JonathanXLin/SmartSwitch/photos/raw/DSC_2327.JPG

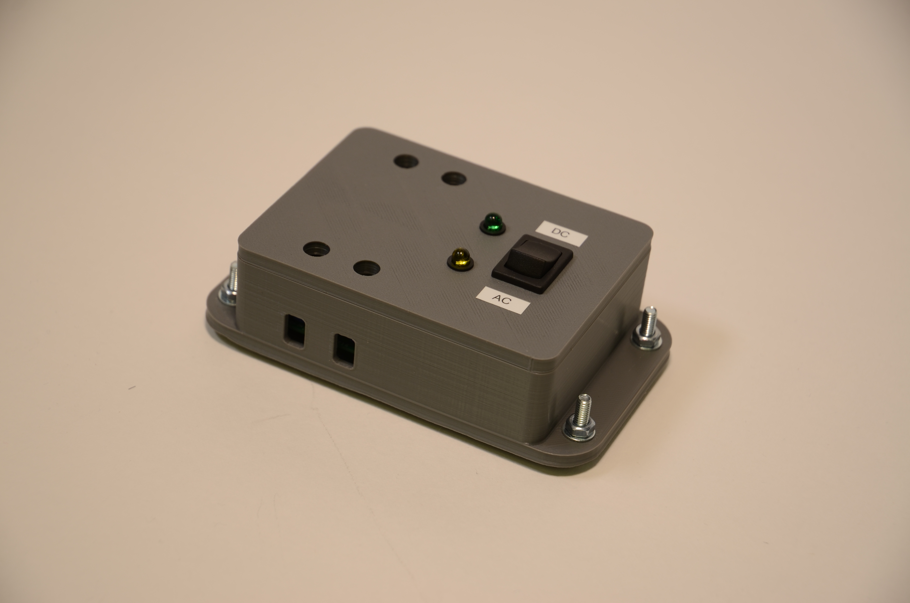
photos/raw/DSC_2327.JPG
