JonathanXLin/SmartSwitch/photos/raw/DSC_2328.JPG

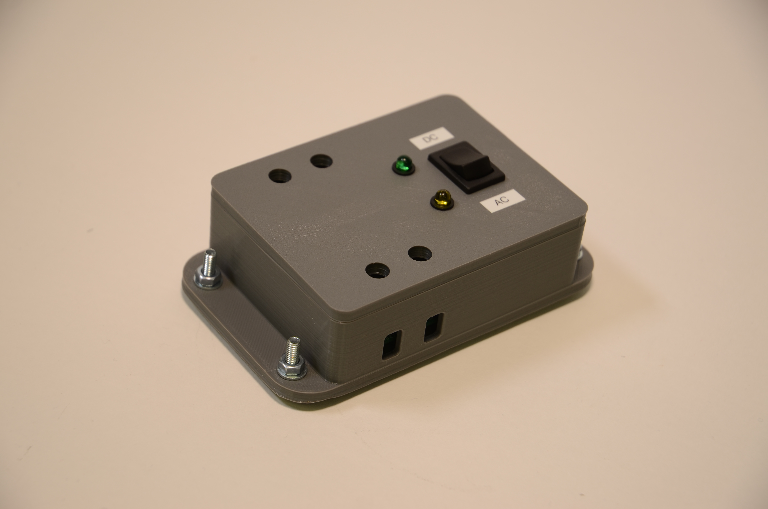
photos/raw/DSC_2328.JPG
