JonathanXLin/SmartSwitch/photos/raw/DSC_2329.JPG

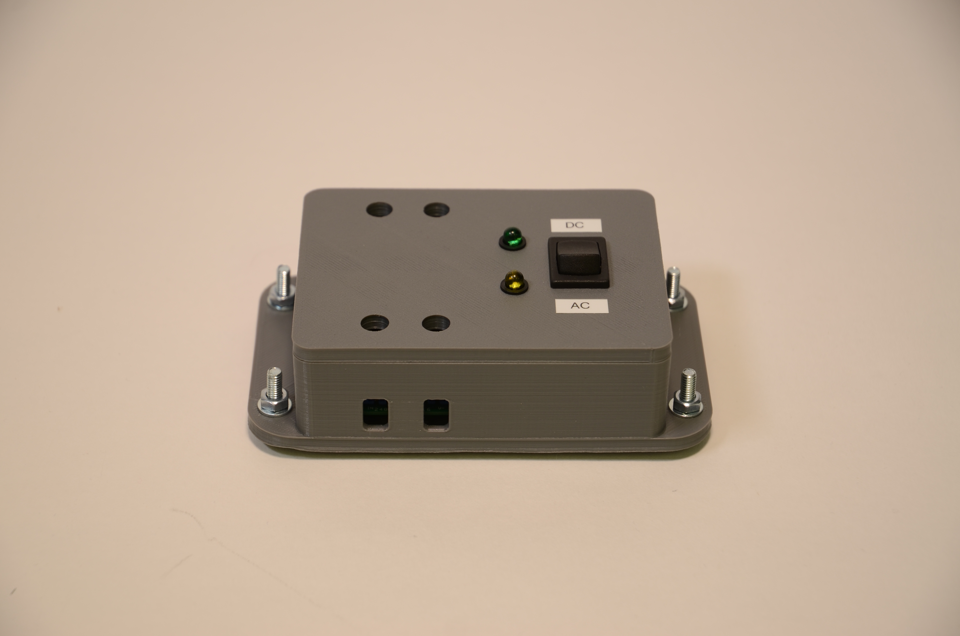
photos/raw/DSC_2329.JPG
