JonathanXLin/SmartSwitch/photos/raw/DSC_2330.JPG

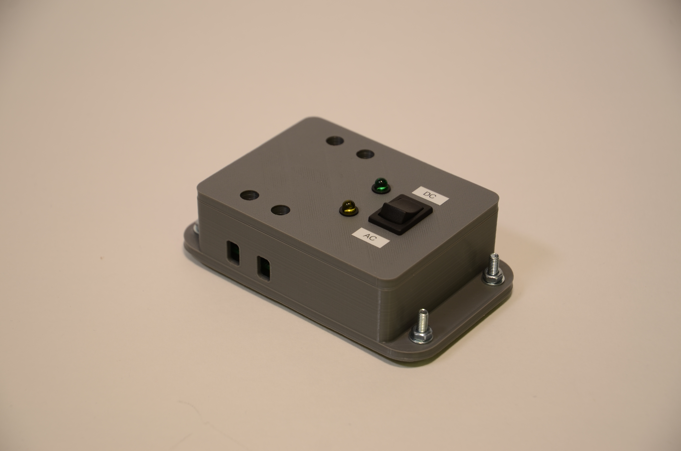
photos/raw/DSC_2330.JPG
