JonathanXLin/SmartSwitch/photos/raw/DSC_2331.JPG

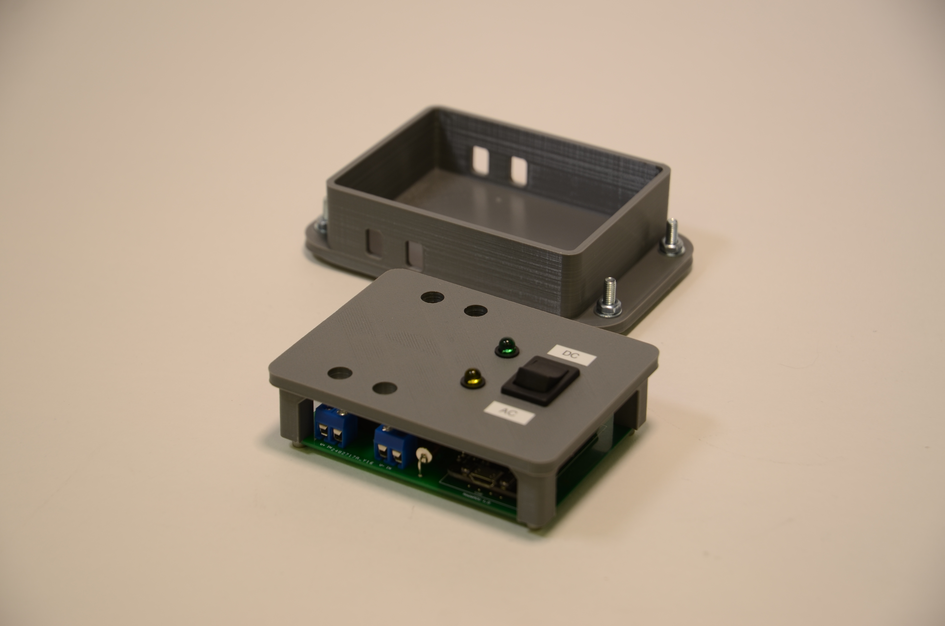
photos/raw/DSC_2331.JPG
