JonathanXLin/SmartSwitch/photos/raw/DSC_2333.JPG

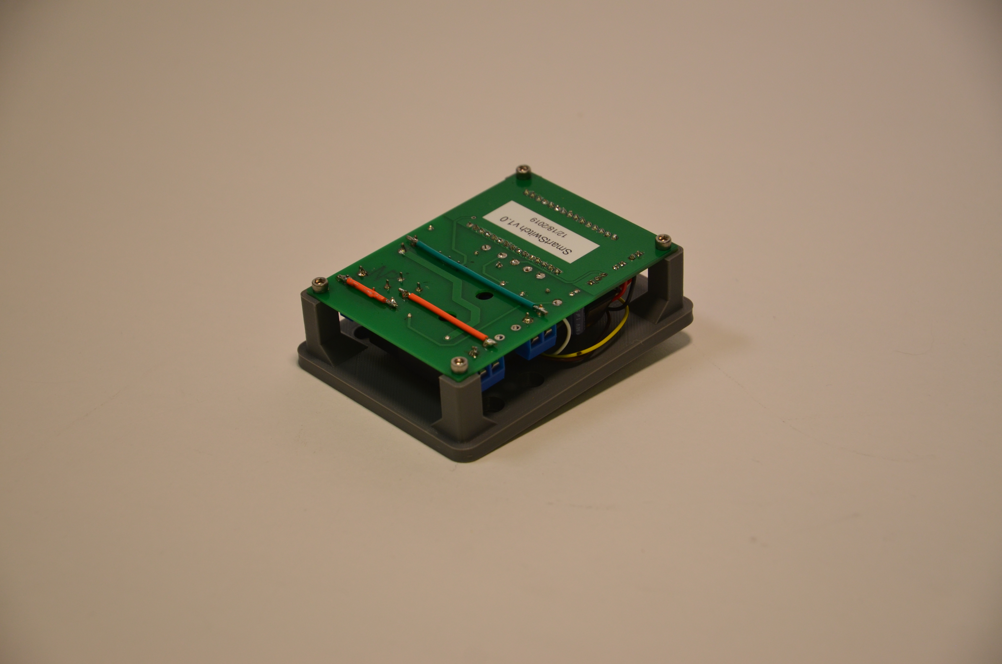
photos/raw/DSC_2333.JPG
