JonathanXLin/SmartSwitch/photos/raw/DSC_2334.JPG

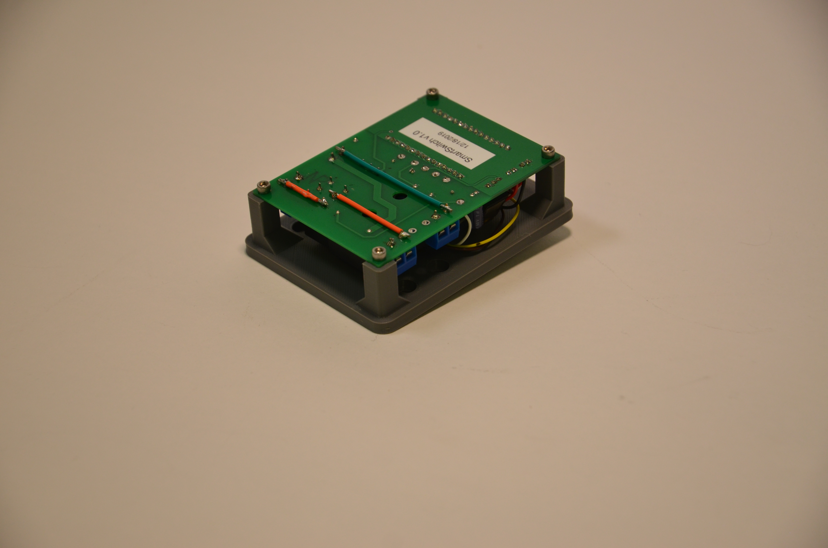
photos/raw/DSC_2334.JPG
